jrbe/2-Coil-Economizer-PCB/PWM Economizer/PWM Economizer/Images/Dimensions.PNG

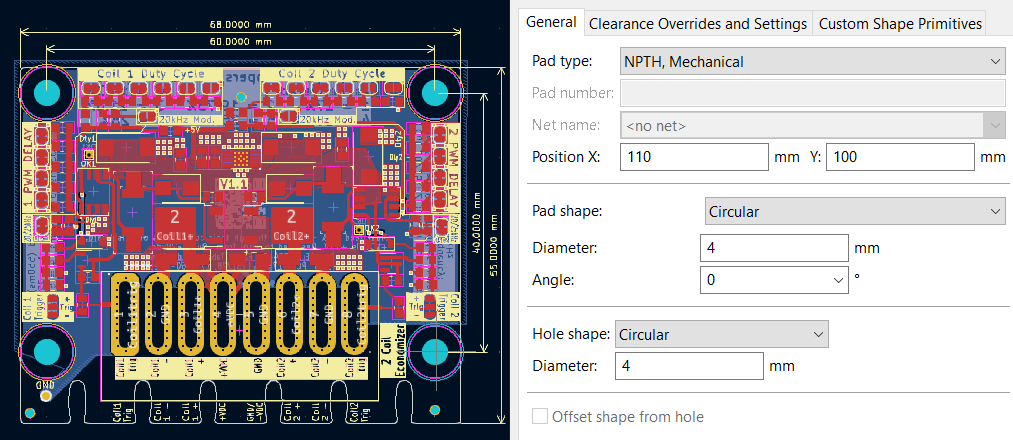
PWM Economizer/PWM Economizer/Images/Dimensions.PNG
