jrbe/2-Coil-Economizer-PCB/PWM Economizer/PWM Economizer/Images/V0.0/PCB Editor.PNG

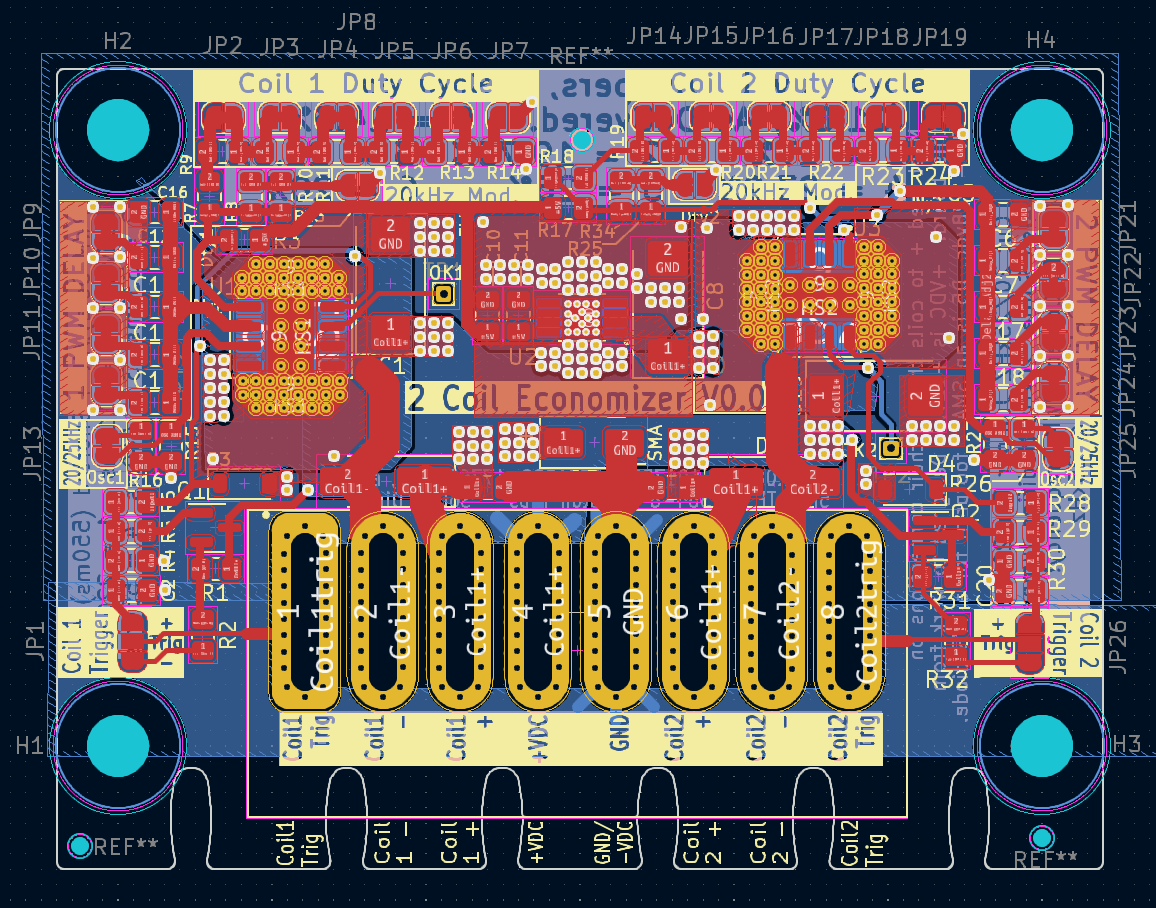
PWM Economizer/PWM Economizer/Images/V0.0/PCB Editor.PNG
