jrbe/2-Coil-Economizer-PCB/PWM Economizer/PWM Economizer/Images/V1.1 Top Populated.PNG

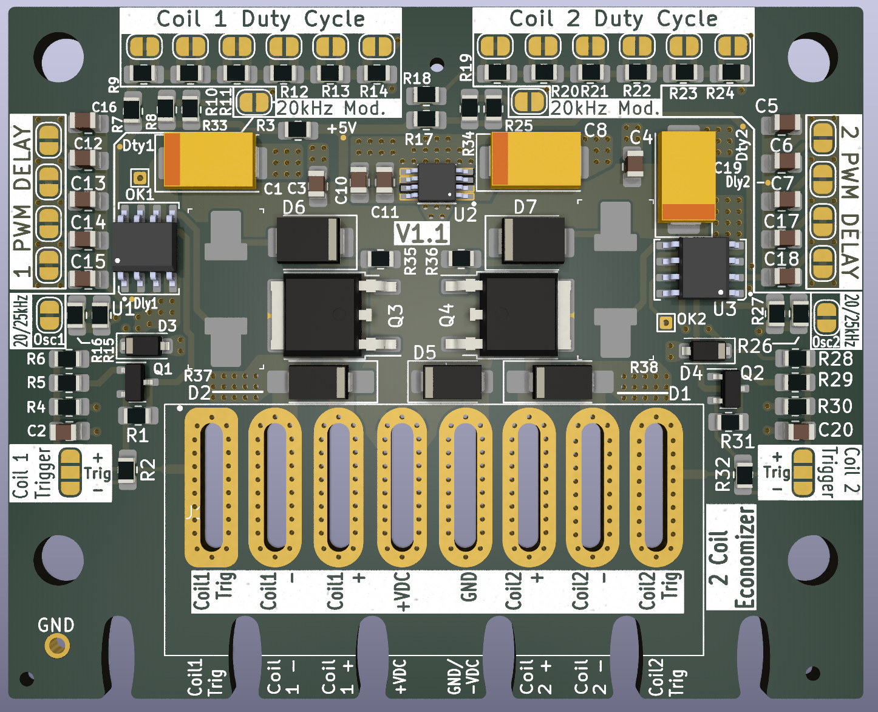
PWM Economizer/PWM Economizer/Images/V1.1 Top Populated.PNG
