jrbe/2-Coil-Economizer-PCB/PWM Economizer/PWM Economizer/Component Files/github.comjrbe2-Coil-Economizer-PCB.png

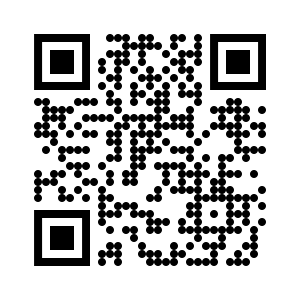
PWM Economizer/PWM Economizer/Component Files/github.comjrbe2-Coil-Economizer-PCB.png
