jrbe/2-Coil-Economizer-PCB/PWM Economizer/PWM Economizer/Images/V0.0/Top W Components.PNG

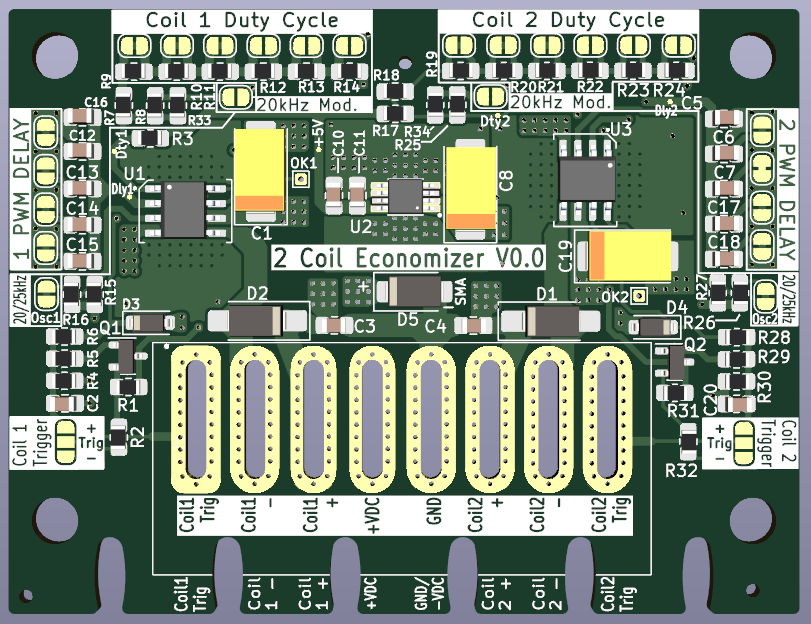
PWM Economizer/PWM Economizer/Images/V0.0/Top W Components.PNG
